transistorfet/synthetik/src/synthetik/YM3812_instruments.h

#ifndef YM3812_instruments_H
#define YM3812_instruments_H

#include "YM3812.h"

struct instrument list[] = {

// From GENMIDI.op2
{ 0x33, 0xa5, 0xe1, 0x23, 0x0e, 0x02, 0x31, 0x25, 0xf1, 0xf4, 0x04, 0x00, 0x00 },    // Acoustic Grand Piano
{ 0x33, 0xa3, 0xf1, 0x33, 0x0c, 0x04, 0x31, 0x23, 0xf1, 0xf4, 0x00, 0x00, 0x00 },    // Bright Acoustic Piano
{ 0x31, 0x1a, 0xe1, 0xb3, 0x08, 0x04, 0x30, 0x9a, 0xf1, 0xf4, 0x00, 0x00, 0x00 },    // Electric Grand Piano
{ 0x31, 0x8e, 0xfa, 0x73, 0x0a, 0x00, 0x11, 0x0e, 0xd1, 0xf4, 0x04, 0x00, 0x00 },    // Honky-tonk Piano
{ 0x16, 0x6f, 0xf2, 0xe7, 0x0c, 0x02, 0x01, 0xaf, 0xf2, 0xb8, 0x00, 0x00, 0x00 },    // Electric Piano (Rhodes)
{ 0x36, 0x9d, 0xf4, 0xc7, 0x0e, 0x02, 0x31, 0x1d, 0xf2, 0xd7, 0x00, 0x00, 0x00 },    // Electric Piano (DX-7)
{ 0x34, 0x51, 0xf1, 0x23, 0x06, 0x05, 0x11, 0x11, 0xd1, 0xf5, 0x04, 0x00, 0x00 },    // Harpsichord
{ 0x01, 0x44, 0xf1, 0x59, 0x06, 0x05, 0x11, 0x04, 0xf1, 0xf7, 0x00, 0x00, 0x00 },    // Clavichord
{ 0x07, 0x54, 0xf6, 0x87, 0x09, 0x00, 0x31, 0x14, 0xf2, 0xe4, 0x00, 0x00, 0x00 },    // Celesta
{ 0x3f, 0xa1, 0xf3, 0xa5, 0x0c, 0x00, 0x12, 0x21, 0xc3, 0xf2, 0x00, 0x00, 0x00 },    // 
{ 0x1a, 0x9e, 0x56, 0x04, 0x08, 0x00, 0x01, 0x1e, 0xf6, 0x04, 0x00, 0x00, 0x00 },    // Music Box
{ 0xb2, 0xe5, 0xf2, 0xf6, 0x0f, 0x00, 0x81, 0x25, 0xf2, 0xf6, 0x00, 0x00, 0x00 },    // 
{ 0x18, 0x63, 0xf6, 0xf6, 0x06, 0x00, 0x00, 0xa3, 0xe5, 0xf7, 0x00, 0x00, 0x00 },    // 
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
{ 0x07, 0x00, 0xf0, 0xf0, 0x00, 0x00, 0x00, 0x00, 0xf6, 0xb4, 0x00 },    // VLNPIZZ1
{ 0x07, 0x1f, 0xf5, 0xfa, 0x00, 0x00, 0x00, 0x57, 0xf5, 0xfa, 0x00 },    // XYLO2
{ 0x03, 0x4f, 0xf1, 0x53, 0x00, 0x00, 0x01, 0x00, 0xf2, 0x74, 0x00 },    // XYLO3
*/
};


#endif
