transistorfet/synthetik/tests/ym3812-sound.c

#define SERIAL_SPEED	115200


#define YM_LDATA_PORT	PORTA
#define YM_LDATA_PIN	PINA
#define YM_LDATA_DDR	DDRA

#define YM_CS		38
#define YM_RD		39
#define YM_WR		40
#define YM_A0		41
#define YM_RESET	50


#undef INLINE_NOP
#define INLINE_NOP		__asm__("nop\n\t");



/******************************
 * Serial Communications Code *
 ******************************/

#define SERIAL_SIZE	64

char serial_read_tail = 0;
char serial_read_head = 0;
char serial_avail = 0;
char serial_rb[SERIAL_SIZE];
char serial_write_head = 0;
char serial_write_tail = 0;
char serial_wb[SERIAL_SIZE];

byte read_serial()
{
	register char b;

	b = Serial.read();
	if (b == -1)
		return 0;

	noInterrupts();
	serial_rb[serial_read_tail] = b;
	if (b == '\n' || b == '\r') {
		serial_rb[serial_read_tail] = '\0';
		serial_avail = 1;
	}
	if (serial_read_tail < SERIAL_SIZE)
		serial_read_tail++;
	interrupts();
	return serial_avail;
}

inline byte serial_get_byte()
{
	register byte value;

	noInterrupts();
	if (serial_read_head == serial_read_tail) {
		//clear_read_buffer();
		value = -1;
	} else {
		value = serial_rb[serial_read_head++];
		if (serial_read_head >= SERIAL_SIZE)
			serial_read_head = 0;
	}
	interrupts();
	return value;
}

inline byte serial_add_byte(byte data)
{
	noInterrupts();
	serial_wb[serial_write_tail++] = data;
	interrupts();
}

void clear_read_buffer()
{
	noInterrupts();
	serial_avail = 0;
	serial_read_head = 0;
	serial_read_tail = 0;
	interrupts();
}

void flush_write_buffer()
{
	if (serial_write_tail > 0) {
		noInterrupts();
		for (byte i = 0; i < serial_write_tail; i++) {
			Serial.write(serial_wb[i]);
		}
		serial_write_head = 0;
		serial_write_tail = 0;
		interrupts();
	}
}


/**********************
 * Audio Control Code *
 **********************/

/*
byte read_data(byte addr)
{
	byte value;

	YM_LDATA_DDR = 0xFF;
	YM_LDATA_PORT = addr;

	digitalWrite(YM_BC1, 1);
	digitalWrite(YM_BDIR, 1);
	delayMicroseconds(15);
	digitalWrite(YM_BC1, 0);
	digitalWrite(YM_BDIR, 0);

	YM_LDATA_DDR = 0x00;
	YM_LDATA_PORT = 0x00;

	digitalWrite(YM_BC1, 1);
	digitalWrite(YM_BDIR, 0);
	delayMicroseconds(1);
	value = YM_LDATA_PIN;
	digitalWrite(YM_BC1, 0);
	digitalWrite(YM_BDIR, 0);

	YM_LDATA_DDR = 0xFF;

	return value;
}
*/

void write_data(byte addr, byte data)
{
	// Output to data bus
	YM_LDATA_DDR = 0xFF;
	digitalWrite(YM_CS, 0);

	// A0=0 to select register
	digitalWrite(YM_A0, 0);
	YM_LDATA_PORT = addr;

	// Write register value
	digitalWrite(YM_WR, 0);
	delayMicroseconds(1);
	digitalWrite(YM_WR, 1);
	delayMicroseconds(5);

	// A0=1 to write data
	digitalWrite(YM_A0, 1);
	YM_LDATA_PORT = data;

	// Write data value
	digitalWrite(YM_WR, 0);
	delayMicroseconds(1);
	digitalWrite(YM_WR, 1);
	delayMicroseconds(23);

	digitalWrite(YM_CS, 1);
	digitalWrite(YM_A0, 0);
}

void set_tone(byte channel, word tone)
{
	write_data(0 + (channel * 2), tone & 0xff);
	write_data(1 + (channel * 2), (tone >> 8) & 0xff);
}

#define CLOCK	3686400

#define NOTE_C3		(CLOCK / (16 * 130.81))
#define NOTE_D3		(CLOCK / (16 * 146.83))
#define NOTE_E3		(CLOCK / (16 * 164.81))
#define NOTE_F3		(CLOCK / (16 * 174.61))
#define NOTE_G3		(CLOCK / (16 * 196.00))
#define NOTE_A3		(CLOCK / (16 * 220.00))
#define NOTE_B3		(CLOCK / (16 * 246.94))
#define NOTE_C4		(CLOCK / (16 * 261.63))
#define NOTE_D4		(CLOCK / (16 * 293.66))
#define NOTE_E4		(CLOCK / (16 * 329.63))
#define NOTE_F4		(CLOCK / (16 * 349.23))
#define NOTE_G4		(CLOCK / (16 * 392.00))

void init_audio()
{
	digitalWrite(YM_RESET, 0);
	delay(10);
	digitalWrite(YM_RESET, 1);

	write_data(0x01, 0x10);

	write_data(0x20, 0x01);		// Set the modulator's multiple to 1
	write_data(0x40, 0x10);		// Set the modulator's level to about 40 dB
	write_data(0x60, 0xF0);		// Modulator attack:  quick;   decay:   long
	write_data(0x80, 0x77);		// Modulator sustain: medium;  release: medium
	write_data(0xA0, 0x98);		// Set voice frequency's LSB (it'll be a D#)
	write_data(0x23, 0x01);		// Set the carrier's multiple to 1
	write_data(0x43, 0x00);		// Set the carrier to maximum volume (about 47 dB)
	write_data(0x63, 0xF0);		// Carrier attack:  quick;   decay:   long
	write_data(0x83, 0x77);		// Carrier sustain: medium;  release: medium
	write_data(0xB0, 0x31);		// Turn the voice on; set the octave and freq MSB

/*
	write_data(0x22, 0);
	write_data(0x27, 0);
	write_data(0x28, 0);
	write_data(0x28, 1);
	write_data(0x28, 2);
	write_data(0x28, 3);
	write_data(0x28, 4);
	write_data(0x28, 5);
	write_data(0x28, 6);
	write_data(0x2B, 0);
	write_data(0x30, 0x71);
	write_data(0x34, 0x0D);
	write_data(0x38, 0x33);
	write_data(0x3C, 0x01);
	write_data(0x40, 0x23);
	write_data(0x44, 0x2D);
	write_data(0x48, 0x26);
	write_data(0x4C, 0x00);
	write_data(0x50, 0x5F);
	write_data(0x54, 0x99);
	write_data(0x58, 0x5F);
	write_data(0x5C, 0x94);
	write_data(0x60, 5);
	write_data(0x64, 5);
	write_data(0x68, 5);
	write_data(0x6C, 7);
	write_data(0x70, 2);
	write_data(0x74, 2);
	write_data(0x78, 2);
	write_data(0x7C, 2);
	write_data(0x80, 0x11);
	write_data(0x84, 0x11);
	write_data(0x88, 0x11);
	write_data(0x8C, 0xA6);
	write_data(0x90, 0);
	write_data(0x94, 0);
	write_data(0x98, 0);
	write_data(0x9C, 0);
	write_data(0xB0, 0x32);
	write_data(0xB4, 0xC0);
	write_data(0x28, 0x00);

	write_data(0xA4, 0x22);
	write_data(0xA0, 0x69);
	write_data(0x28, 0xF0);
*/

/*
	digitalWrite(YM_RESET, 0);
	delayMicroseconds(15);
	digitalWrite(YM_RESET, 1);

	write_data(7, 0x3E);
	write_data(8, 0x0F);
	write_data(9, 0x00);
	write_data(10, 0x00);
	set_tone(0, 0);

	Serial.println(read_data(7), HEX);
	Serial.println(read_data(10), HEX);
	Serial.println(read_data(15), HEX);
*/
}

void run_reset()
{
	init_audio();
}

void run_test()
{

/*
	write_data(13, 0xFF);
	write_data(14, 0xFF);
	write_data(15, 0x00);

	set_tone(0, NOTE_E4);
	delay(200);
	set_tone(0, 0);
	delay(20);

	set_tone(0, NOTE_E4);
	delay(150);
	set_tone(0, 0);
	delay(20);

	set_tone(0, NOTE_E4);
	delay(150);
	set_tone(0, 0);
	delay(20);

	delay(100);

	set_tone(0, NOTE_C4);
	delay(100);
	set_tone(0, 0);
	delay(20);

	set_tone(0, NOTE_E4);
	delay(100);
	set_tone(0, 0);
	delay(20);

	delay(200);

	set_tone(0, NOTE_G4);
	delay(200);
	set_tone(0, 0);
	delay(20);

	delay(200);

	set_tone(0, NOTE_G3);
	delay(200);
	set_tone(0, 0);
	delay(20);
*/
}

void run_mute()
{
	write_data(7, 0x3F);
}

void run_unmute()
{
	write_data(7, 0x3E);
}




void do_command(String line)
{
	if (line.equals("test")) {
		run_test();
	}
	else if (line.equals("mute")) {
		run_mute();
	}
	else if (line.equals("unmute")) {
		run_unmute();
	}
	else if (line.equals("reset")) {
		run_reset();
	}
	else {
		Serial.println("No such command");
	}
}

void setup()
{
	Serial.begin(SERIAL_SPEED);

	pinMode(13, OUTPUT);
	digitalWrite(13, 0);

	// Controls
	pinMode(YM_CS, OUTPUT);
	pinMode(YM_RD, OUTPUT);
	pinMode(YM_WR, OUTPUT);
	pinMode(YM_A0, OUTPUT);
	pinMode(YM_RESET, OUTPUT);
	digitalWrite(YM_CS, 1);
	digitalWrite(YM_RD, 1);
	digitalWrite(YM_WR, 1);
	digitalWrite(YM_A0, 0);
	digitalWrite(YM_RESET, 1);

	// Data Bus
	YM_LDATA_PORT = 0x00;	// D0 - D7
	YM_LDATA_DDR = 0x00;

	init_audio();

	Serial.print("> ");
}

void loop()
{
	//String line = Serial.readString();
	//do_command(line);

	//flush_write_buffer();

	if (read_serial()) {
		String line = String(serial_rb);
		clear_read_buffer();
		Serial.print(line);
		Serial.print("\n");
		do_command(line);
		Serial.print("\n> ");
	}
}
